hlohse/dj-glove/Arduino/DjGlove/Poti.h

#ifndef DJ_GLOVE_ARDUINO_DJ_GLOVE_POTI_H_
#define DJ_GLOVE_ARDUINO_DJ_GLOVE_POTI_H_

class Poti {
public:
  Poti(const byte pin)
  : m_pin(pin)
  {
    pinMode(m_pin, INPUT);
  }
  
  int read() const
  {
    // Adjust 0..1023 to 0..127
    const int value = analogRead(m_pin) / 8;
    
    // Invert value range so that poti totally left = 0, right = 127
    return 127 - value;
  }

private:
  byte m_pin;
};

#endif // DJ_GLOVE_ARDUINO_DJ_GLOVE_POTI_H_
