hlohse/dj-glove/Arduino/DjGlove/Push.h

#ifndef DJ_GLOVE_ARDUINO_DJ_GLOVE_PUSH_H_
#define DJ_GLOVE_ARDUINO_DJ_GLOVE_PUSH_H_

class Push {
public:
  Push(const byte pin)
  : m_pin(pin),
    m_num_debounces(0)
  {
    pinMode(m_pin, INPUT);
  }
  
  bool isPushed()
  {
    const bool is_pushed = digitalRead(m_pin) == HIGH;
    
    if (!is_pushed) {
      m_num_debounces = 0;
      return false;
    }
    
    if (m_num_debounces < necessary_debounces) {
      m_num_debounces++;
    }
      
    return m_num_debounces == necessary_debounces;
  }

private:
  static const int necessary_debounces = 5;
  
  byte m_pin;
  int  m_num_debounces;
};

#endif // DJ_GLOVE_ARDUINO_DJ_GLOVE_PUSH_H_
